pjgpetecodes/pico-streamdeck/keycaps/1person(Big).png

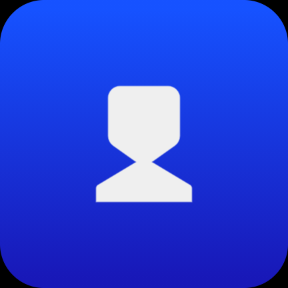
keycaps/1person(Big).png
