pjgpetecodes/pico-streamdeck/keycaps/1person-share(Big).png

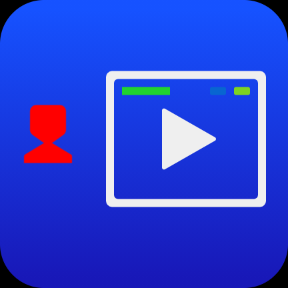
keycaps/1person-share(Big).png
