pjgpetecodes/pico-streamdeck/keycaps/2people(Big).png

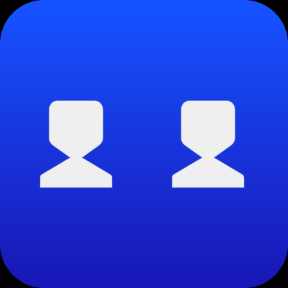
keycaps/2people(Big).png
