pjgpetecodes/pico-streamdeck/keycaps/2people-botshare(Big).png

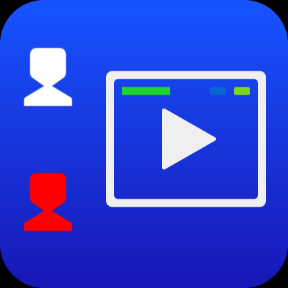
keycaps/2people-botshare(Big).png
