pjgpetecodes/pico-streamdeck/keycaps/3people(big).png

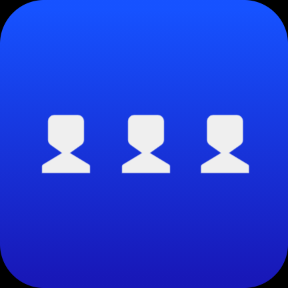
keycaps/3people(big).png
