pjgpetecodes/pico-streamdeck/keycaps/3people-topshare(Big).png

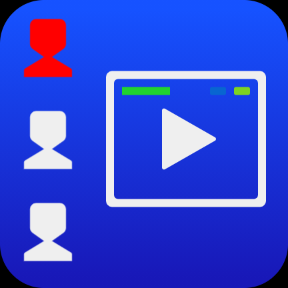
keycaps/3people-topshare(Big).png
