pjgpetecodes/pico-streamdeck/keycaps/KeyCaps.png

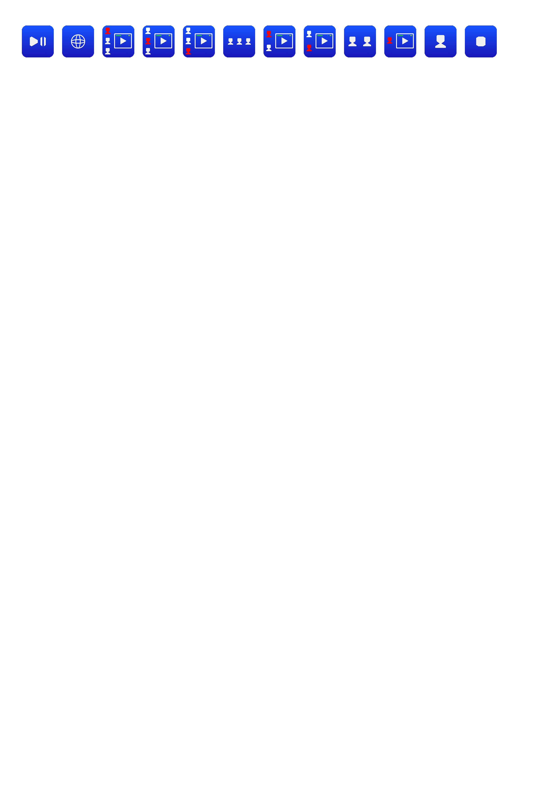
keycaps/KeyCaps.png
