pjgpetecodes/pico-streamdeck/keycaps/start(Big).png

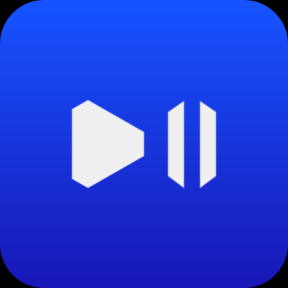
keycaps/start(Big).png
